Wii-Mini-Hacking/miniRGBii/images/output_layer_images/miniRGBii-B_Cu.pdf

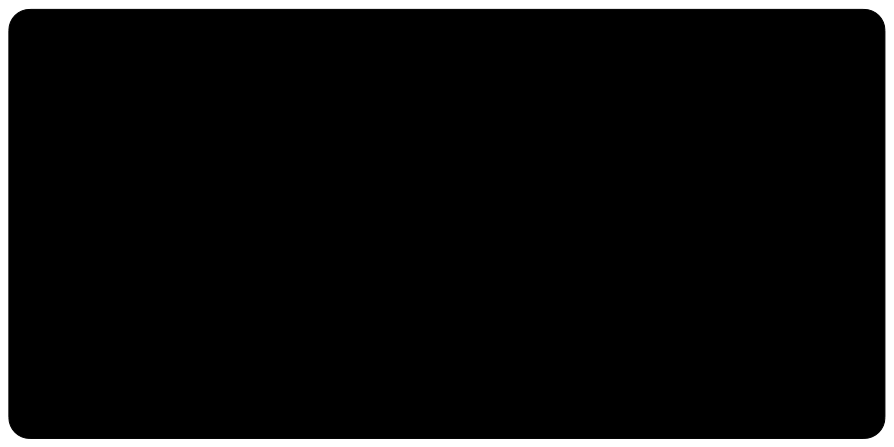
[picture p13: page 1]
