Wii-Mini-Hacking/miniRGBii/images/output_layer_images/miniRGBii-B_Silkscreen.pdf

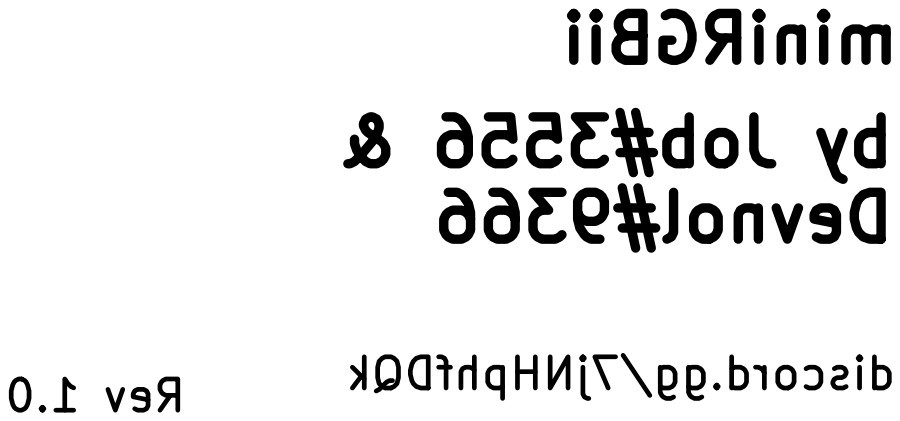
[picture p14: page 1]
