Wii-Mini-Hacking/miniRGBii/images/output_layer_images/miniRGBii-Edge_Cuts.pdf

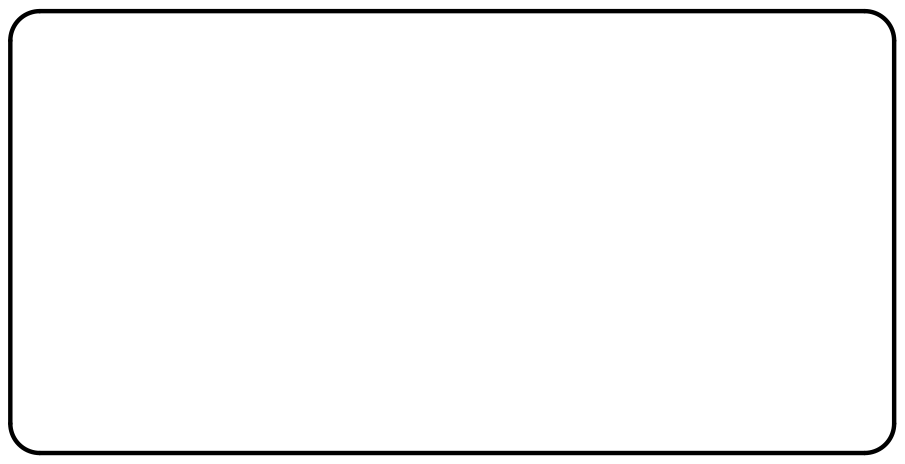
[picture p15: page 1]
