Wii-Mini-Hacking/miniRGBii/images/output_layer_images/miniRGBii-F_Cu.pdf

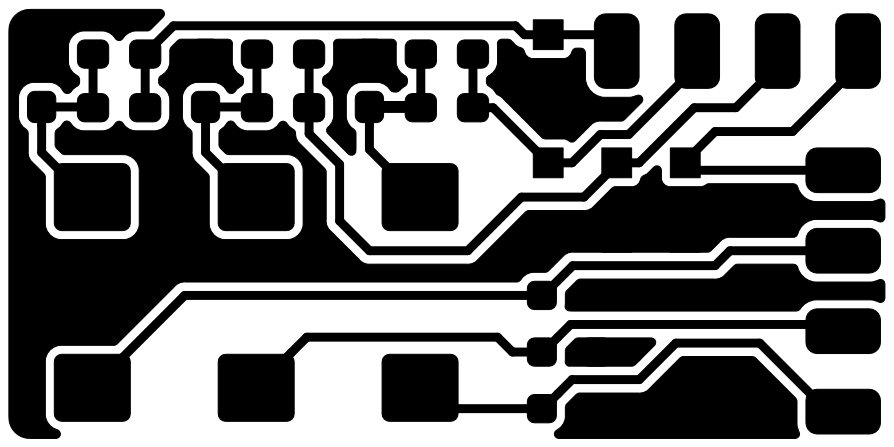
[picture p16: page 1]
