Wii-Mini-Hacking/miniRGBii/images/output_layer_images/miniRGBii-F_Mask.pdf

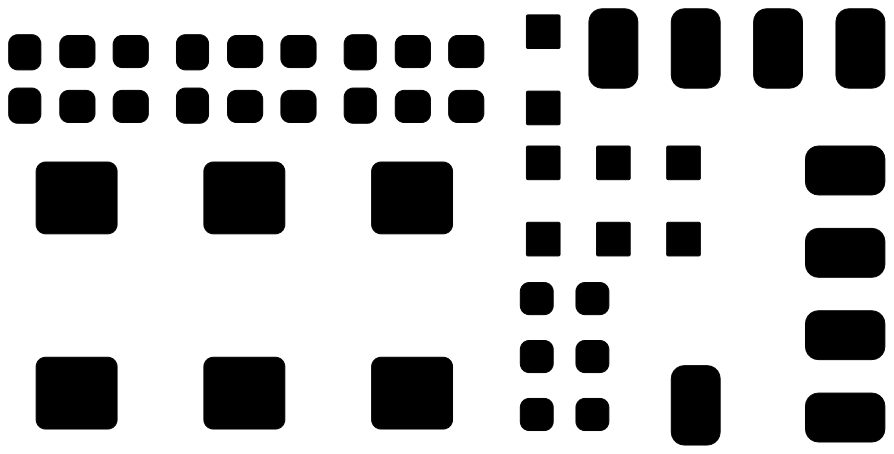
[picture p17: page 1]
