Wii-Mini-Hacking/miniRGBii/images/output_layer_images/miniRGBii-F_Silkscreen.pdf

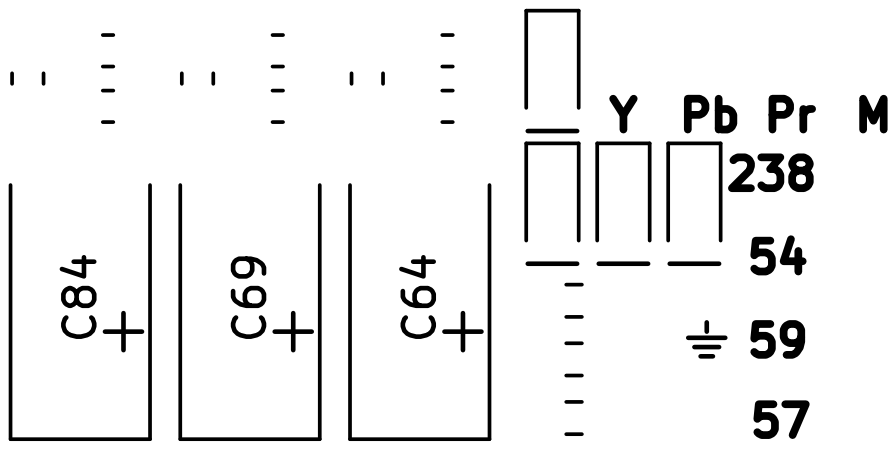
[picture p18: page 1]
